connornishijima/SensoryBridge/extras/img/4.jpg

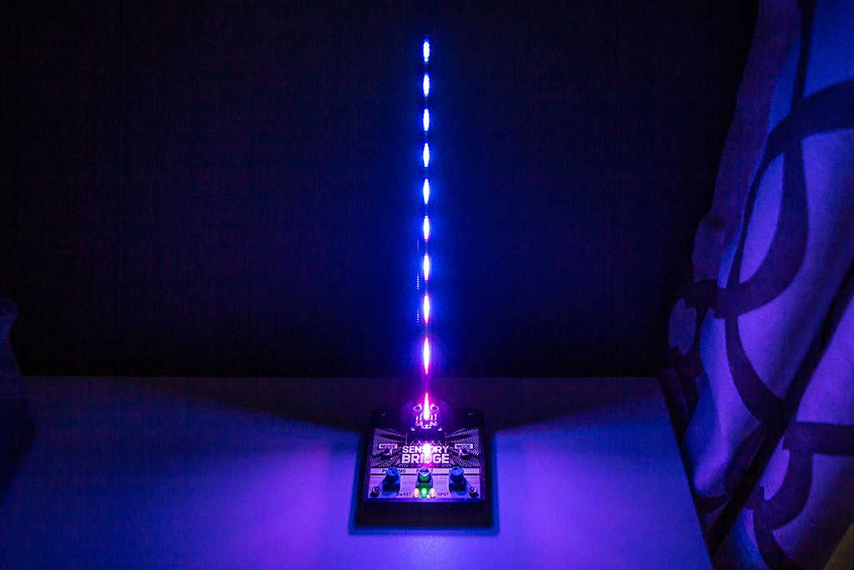
extras/img/4.jpg
