connornishijima/SensoryBridge/extras/img/5.jpg

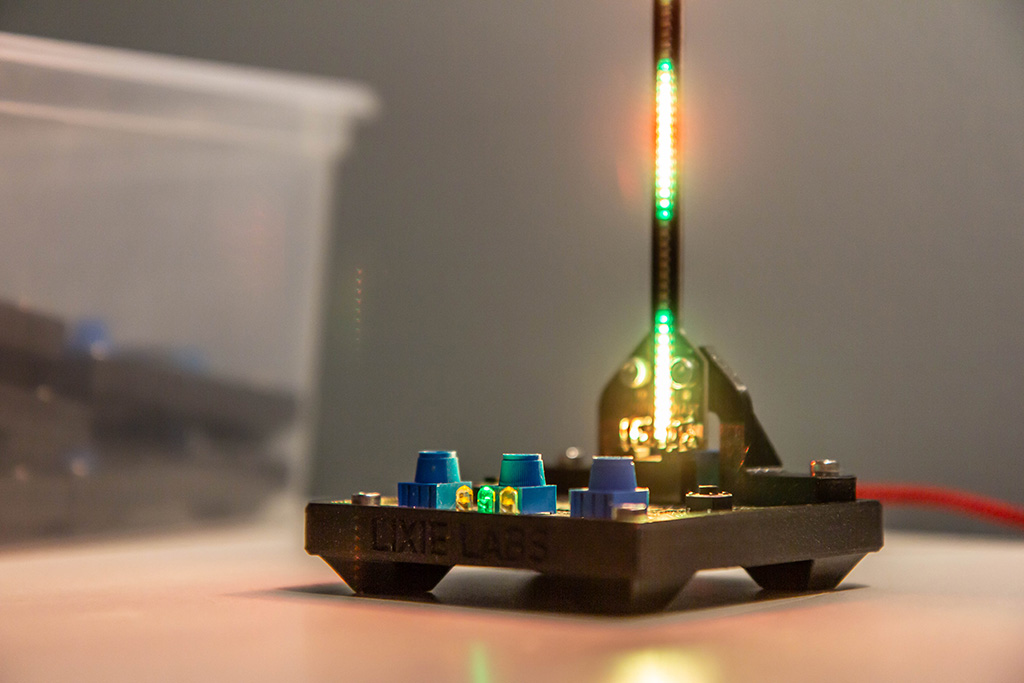
extras/img/5.jpg
