connornishijima/SensoryBridge/extras/img/6.jpg

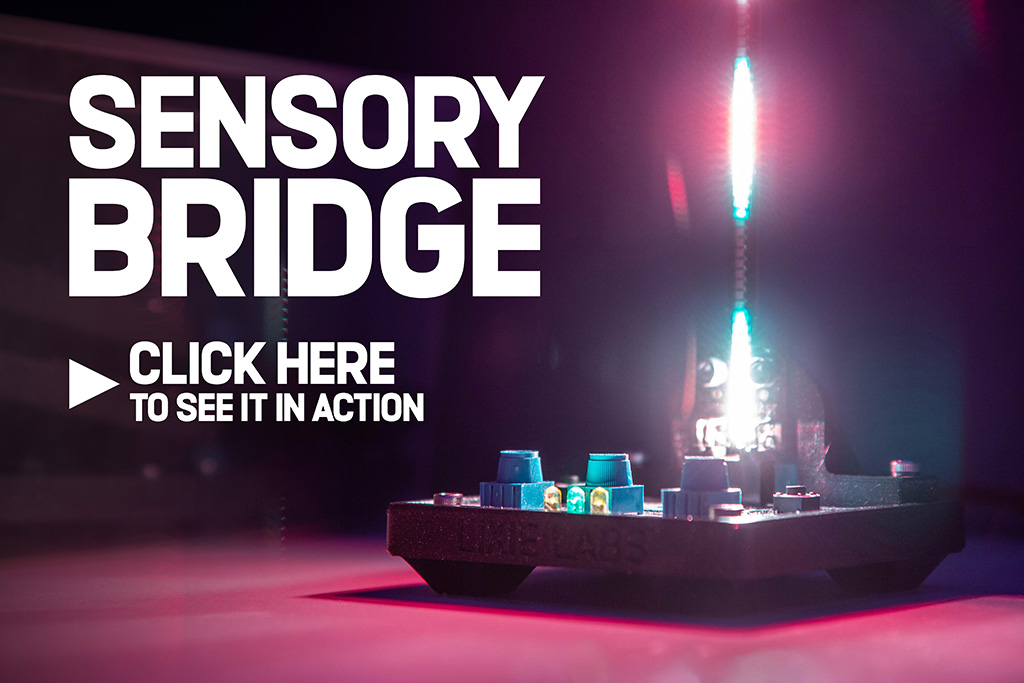
extras/img/6.jpg
