connornishijima/SensoryBridge/extras/img/7.jpg

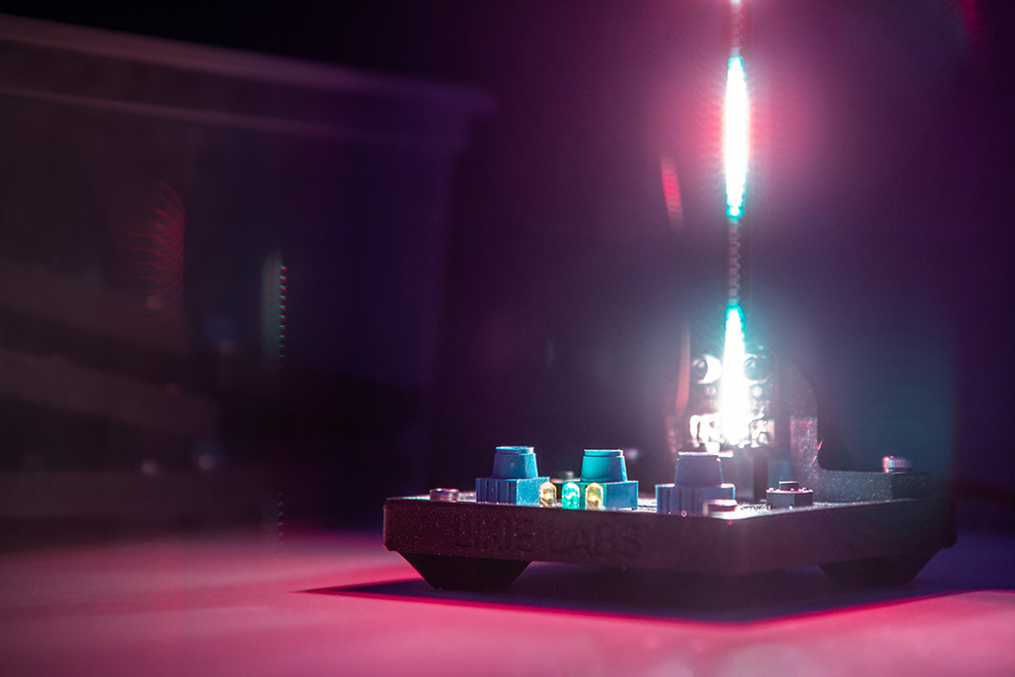
extras/img/7.jpg
