connornishijima/SensoryBridge/extras/img/9.jpg

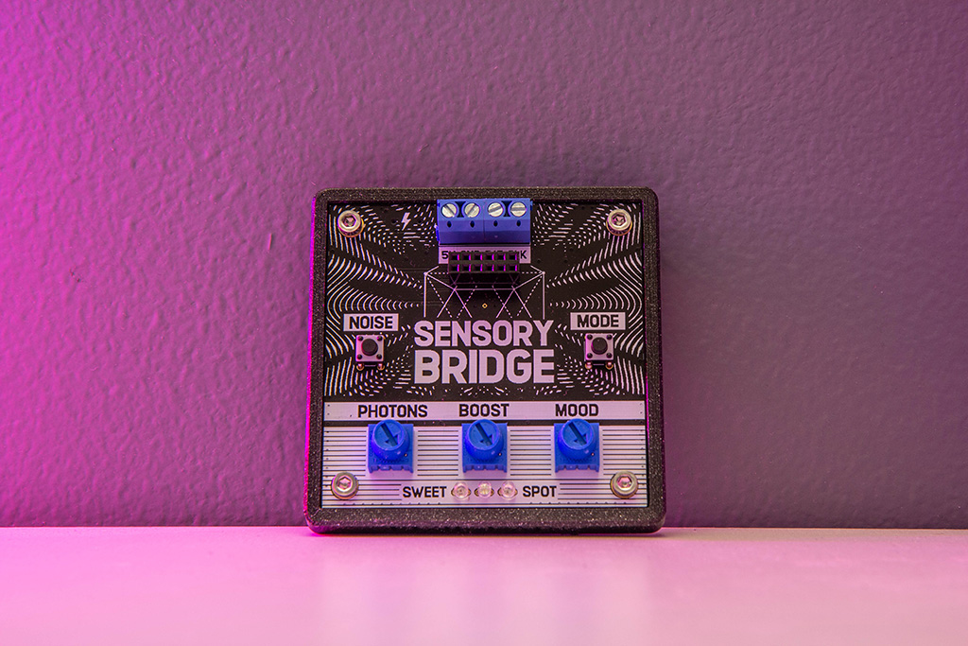
extras/img/9.jpg
