connornishijima/SensoryBridge/extras/img/10.jpg

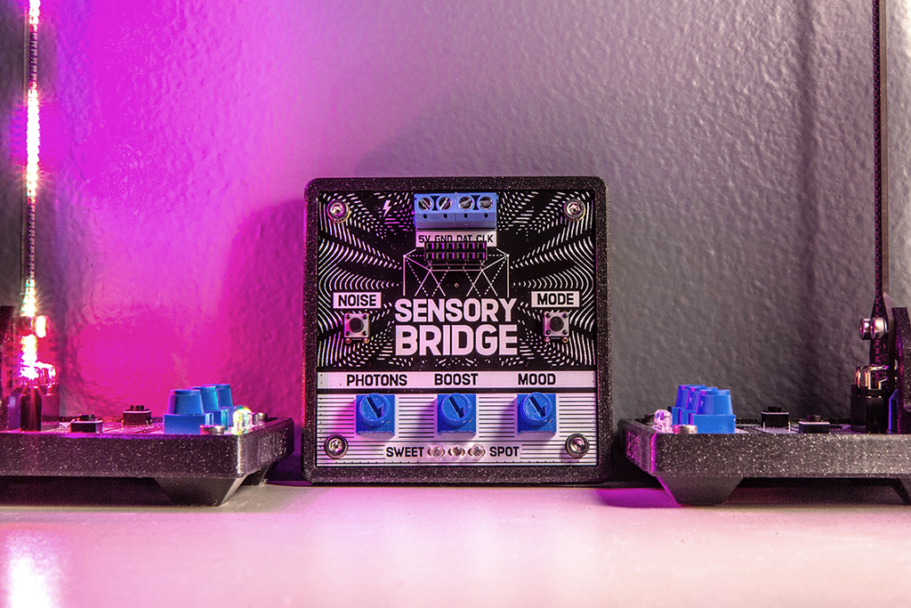
extras/img/10.jpg
