connornishijima/SensoryBridge/extras/img/11.jpg

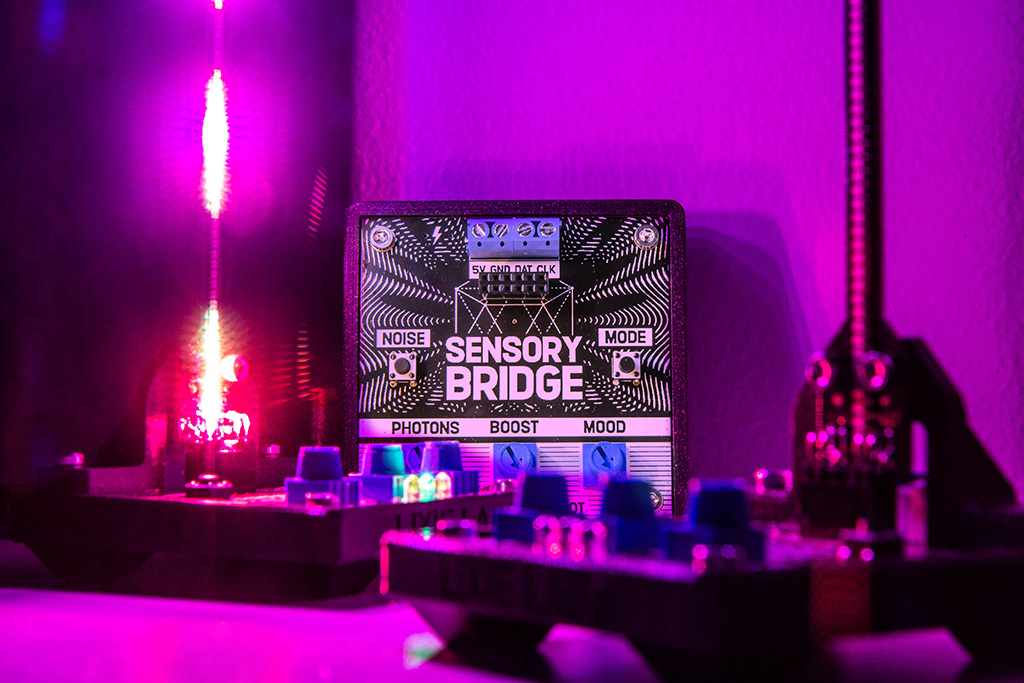
extras/img/11.jpg
