connornishijima/SensoryBridge/extras/img/13.jpg

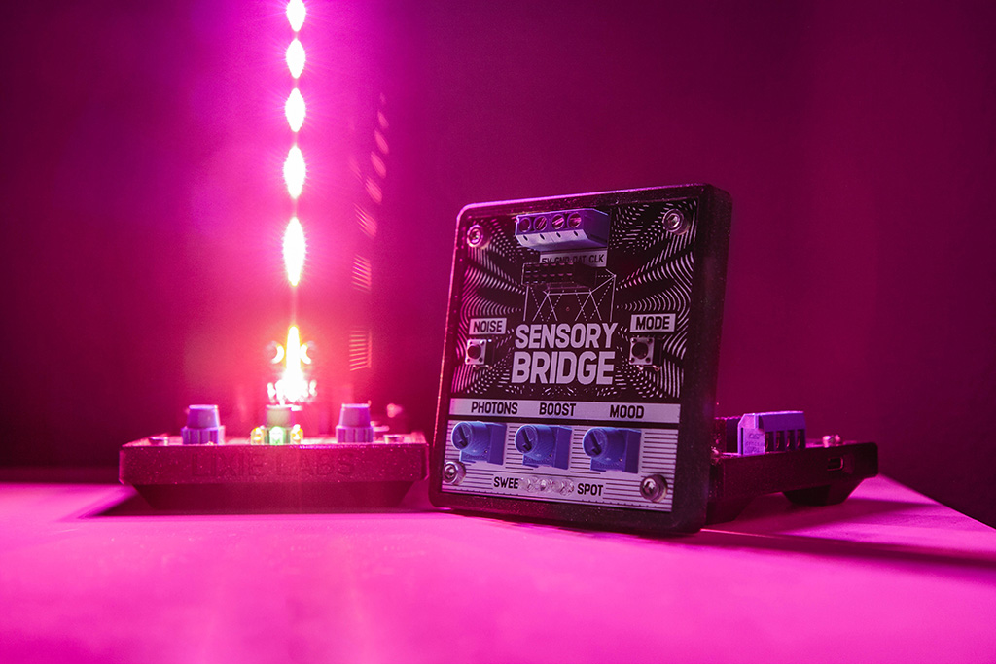
extras/img/13.jpg
