connornishijima/SensoryBridge/extras/img/14.jpg

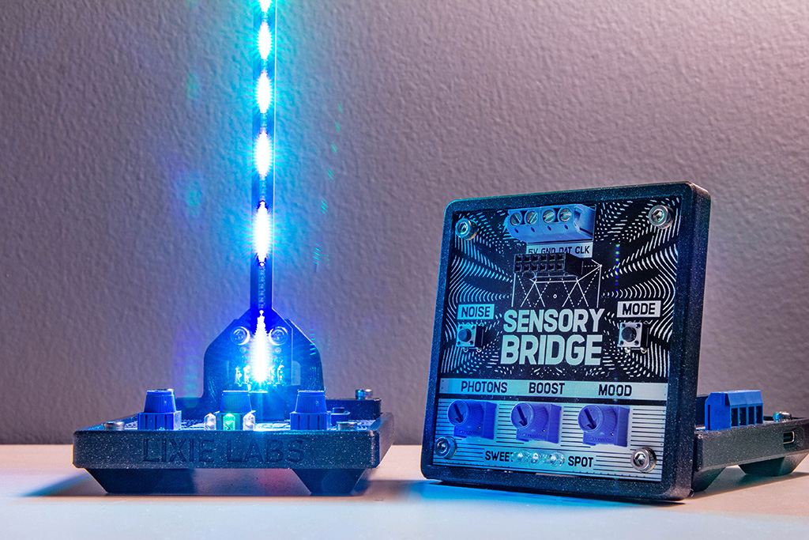
extras/img/14.jpg
