connornishijima/SensoryBridge/extras/img/17.png

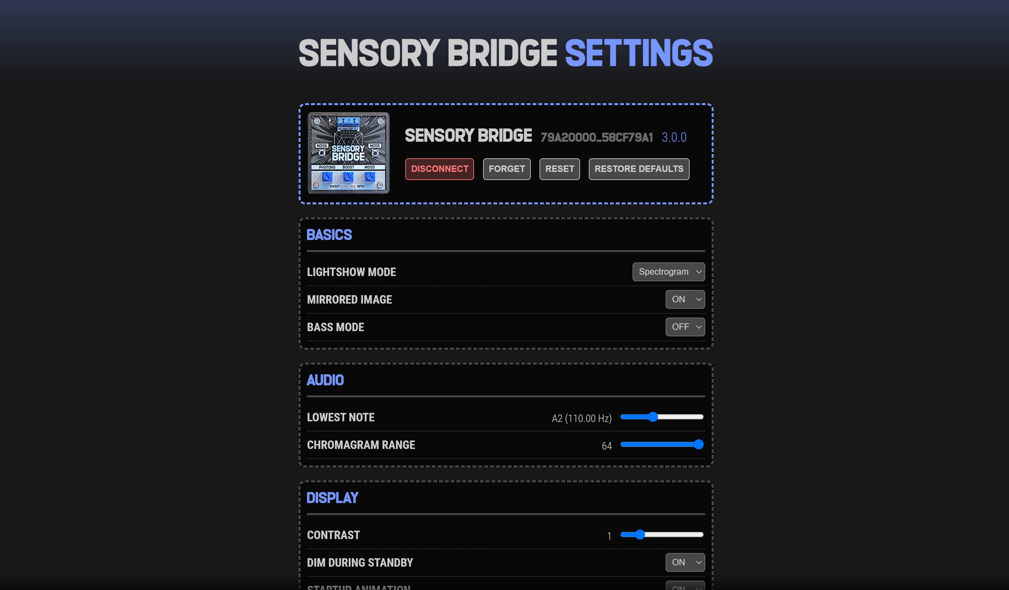
extras/img/17.png
