connornishijima/SensoryBridge/extras/img/firmware_settings.png

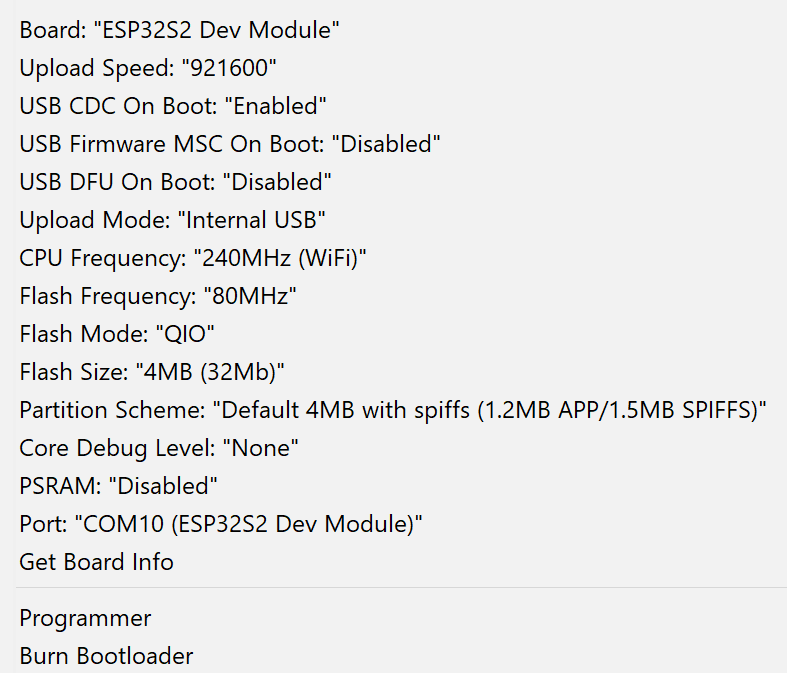
extras/img/firmware_settings.png
