connornishijima/SensoryBridge/SENSORY_BRIDGE_FIRMWARE/bridge_fs.h

/*----------------------------------------
  Sensory Bridge FILESYSTEM ACCESS
  ----------------------------------------*/

extern void reboot(); // system.h

void update_config_filename(uint32_t input) {
  snprintf(config_filename, 24, "/CONFIG_%05lu.BIN", input);
}

// Restore all defaults defined in globals.h by removing saved data and rebooting
void factory_reset() {
  lock_leds();
  USBSerial.print("Deleting ");
  USBSerial.print(config_filename);
  USBSerial.print(": ");

  if (LittleFS.remove(config_filename)) {
    USBSerial.println("file deleted");
  } else {
    USBSerial.println("delete failed");
  }

  USBSerial.print("Deleting noise_cal.bin: ");
  if (LittleFS.remove("/noise_cal.bin")) {
    USBSerial.println("file deleted");
  } else {
    USBSerial.println("delete failed");
  }

  reboot();
}

// Restore only configuration defaults
void restore_defaults() {
  lock_leds();
  USBSerial.print("Deleting ");
  USBSerial.print(config_filename);
  USBSerial.print(": ");

  if (LittleFS.remove(config_filename)) {
    USBSerial.println("file deleted");
  } else {
    USBSerial.println("delete failed");
  }

  reboot();
}

// Save configuration to LittleFS
void save_config() {
  lock_leds();
  if (debug_mode) {
    USBSerial.print("LITTLEFS: ");
  }
  File file = LittleFS.open(config_filename, FILE_WRITE);
  if (!file) {
    if (debug_mode) {
      USBSerial.print("Failed to open ");
      USBSerial.print(config_filename);
      USBSerial.println(" for writing!");
    }
    return;
  } else {
    file.seek(0);
    uint8_t config_buffer[512];
    memcpy(config_buffer, &CONFIG, sizeof(CONFIG));

    for (uint16_t i = 0; i < 512; i++) {
      file.write(config_buffer[i]);
    }

    if (debug_mode) {
      USBSerial.print("WROTE ");
      USBSerial.print(config_filename);
      USBSerial.println(" SUCCESSFULLY");
    }
  }
  file.close();
  unlock_leds();
}

// Save configuration to LittleFS 10 seconds from now
void save_config_delayed() {
  if(debug_mode == true){
    USBSerial.println("CONFIG SAVE QUEUED");
  }
  next_save_time = millis()+5000;
  settings_updated = true;
}

// Load configuration from LittleFS
void load_config() {
  lock_leds();
  if (debug_mode) {
    USBSerial.print("LITTLEFS: ");
  }

  bool queue_factory_reset = false;
  File file = LittleFS.open(config_filename, FILE_READ);
  if (!file) {
    if (debug_mode) {
      USBSerial.print("Failed to open ");
      USBSerial.print(config_filename);
      USBSerial.println(" for reading!");
    }
    return;
  } else {
    file.seek(0);
    uint8_t config_buffer[512];
    for (uint16_t i = 0; i < sizeof(CONFIG); i++) {
      config_buffer[i] = file.read();
    }

    memcpy(&CONFIG, config_buffer, sizeof(CONFIG));

    if (debug_mode) {
      USBSerial.println("READ CONFIG SUCCESSFULLY");
    }
  }
  file.close();

  if (queue_factory_reset == true) {
    factory_reset();
  }
  unlock_leds();
}

// Save noise calibration to LittleFS
void save_ambient_noise_calibration() {
  lock_leds();
  if (debug_mode) {
    USBSerial.print("SAVING AMBIENT_NOISE PROFILE... ");
  }
  File file = LittleFS.open("/noise_cal.bin", FILE_WRITE);
  if (!file) {
    if (debug_mode) {
      USBSerial.println("Failed to open file for writing!");
    }
    return;
  }

  bytes_32 temp;

  file.seek(0);
  for (uint16_t i = 0; i < NUM_FREQS; i++) {
    float in_val = float(noise_samples[i]);

    temp.long_val_float = in_val;

    file.write(temp.bytes[0]);
    file.write(temp.bytes[1]);
    file.write(temp.bytes[2]);
    file.write(temp.bytes[3]);
  }

  file.close();
  if (debug_mode) {
    USBSerial.println("SAVE COMPLETE");
  }

  unlock_leds();
}

// Load noise calibration from LittleFS
void load_ambient_noise_calibration() {
  lock_leds();
  if (debug_mode) {
    USBSerial.print("LOADING AMBIENT_NOISE PROFILE... ");
  }
  File file = LittleFS.open("/noise_cal.bin", FILE_READ);
  if (!file) {
    if (debug_mode) {
      USBSerial.println("Failed to open file for reading!");
    }
    return;
  }

  bytes_32 temp;

  file.seek(0);
  for (uint16_t i = 0; i < NUM_FREQS; i++) {
    temp.bytes[0] = file.read();
    temp.bytes[1] = file.read();
    temp.bytes[2] = file.read();
    temp.bytes[3] = file.read();

    noise_samples[i] = SQ15x16(temp.long_val_float);
  }

  file.close();
  if (debug_mode) {
    USBSerial.println("LOAD COMPLETE");
  }

  unlock_leds();
}

// Initialize LittleFS
void init_fs() {
  lock_leds();
  USBSerial.print("INIT FILESYSTEM: ");
  USBSerial.println(LittleFS.begin(true) == true ? PASS : FAIL);

  update_config_filename(FIRMWARE_VERSION);

  load_ambient_noise_calibration();
  load_config();
  unlock_leds();
}
