connornishijima/SensoryBridge/SENSORY_BRIDGE_FIRMWARE/user_config.h

/*----------------------------------------
  Sensory Bridge HARDWARE CONFIGURATION
----------------------------------------*/

// Every notable setting about hardware moved to the settings.sensorybridge.rocks site for now!
// No more hardcoding values for strip length and such

/*----------------------------------------
  Sensory Bridge SOFTWARE CONFIGURATION
----------------------------------------*/

// TODO: CRGBPalette16/lookups in place of all CHSV usage, which defaults
//       to a rainbow but can be swapped with several pre-made themes by
//       commenting/uncommenting one here or selecting via the UART menu
