connornishijima/SensoryBridge/SENSORY_BRIDGE_FIRMWARE/strings.h

#define PASS "PASS"
#define FAIL "FAIL ###################"

char notes_chromatic[12]  = { 'A','A','B','C','C','D','D','E','F','F','G','G' };
char sharps[12]           = { ' ','#',' ',' ','#',' ','#',' ',' ','#',' ','#' };
